Kageyana/RX671_MCR/RX671_MCR/src/smc_gen/r_bsp/board/generic_rx671/r_bsp_config_reference.h

/*
* Copyright (c) 2011 Renesas Electronics Corporation and/or its affiliates
*
* SPDX-License-Identifier: BSD-3-Clause
*/
/***********************************************************************************************************************
* File Name    : r_bsp_config_reference.h
* Device(s)    : RX671
* Description  : The file r_bsp_config.h is used to configure your BSP. r_bsp_config.h should be included
*                somewhere in your package so that the r_bsp code has access to it. This file (r_bsp_config_reference.h)
*                is just a reference file that the user can use to make their own r_bsp_config.h file.
************************************************************************************************************************
* History : DD.MM.YYYY Version  Description
*         : 18.05.2021 1.00     First Release
*         : 30.11.2021 1.01     Added the following macro definition.
*                               - BSP_CFG_CONFIGURATOR_VERSION
*                               - BSP_CFG_CPLUSPLUS
*                               - BSP_CFG_SERIAL_PROGRAMMER_CONECT_ENABLE
*                               - BSP_CFG_ONCHIP_DEBUGGER_CONECT_ENABLE
*                               Changed initial value of the following macro definitions.
*                               - BSP_CFG_MCU_PART_GROUP
*                               - BSP_CFG_MCU_PART_SERIES
*         : 11.02.2022 1.02     Changed initial value of the following macro definitions.
*                               - BSP_CFG_SWINT_UNIT1_ENABLE
*                               - BSP_CFG_SWINT_UNIT2_ENABLE
*         : 25.11.2022 1.03     Modified comment.
*         : 28.02.2023 1.04     Modified comment.
*         : 21.11.2023 1.05     Added the following macro definitions.
*                               - BSP_CFG_BUS_PRIORITY_INITIALIZE_ENABLE
*                               - BSP_CFG_MEMORY_BUS1_PRIORITY
*                               - BSP_CFG_MEMORY_BUS2_PRIORITY
*                               - BSP_CFG_INTERNAL_PERIPHERAL_BUS1_PRIORITY
*                               - BSP_CFG_INTERNAL_PERIPHERAL_BUS2_3_PRIORITY
*                               - BSP_CFG_INTERNAL_PERIPHERAL_BUS4_5_PRIORITY
*                               - BSP_CFG_INTERNAL_PERIPHERAL_BUS6_PRIORITY
*                               - BSP_CFG_EXTERNAL_BUS_PRIORITY
*                               - BSP_CFG_INTERNAL_EXPANSION_BUS_PRIORITY
*                               - BSP_CFG_BOOTLOADER_PROJECT
*         : 27.11.2024 1.06     Changed comment of BSP_CFG_RTC_ENABLE.
*         : 26.02.2025 1.07     Changed the disclaimer.
***********************************************************************************************************************/
#ifndef R_BSP_CONFIG_REF_HEADER_FILE
#define R_BSP_CONFIG_REF_HEADER_FILE

/***********************************************************************************************************************
Configuration Options
***********************************************************************************************************************/

/* NOTE:
   The default settings are the same as when using RSKRX671.
   Change to the settings for the user board.
*/

/* Start up select
   0 = Enable BSP startup program.
   1 = Disable BSP startup program. (e.g. Using user startup program.)
   NOTE: This setting is available only when using CCRX. */
#define BSP_CFG_STARTUP_DISABLE (0)

/* Enter the product part number for your MCU. This information will be used to obtain information about your MCU such 
   as package and memory size.
   To help parse this information, the part number will be defined using multiple macros.
   R 5 F 56 71 E D D FB
   | | | |  |  | | | |  Macro Name                             Description
   | | | |  |  | | | |__BSP_CFG_MCU_PART_PACKAGE             = Package type, number of pins, and pin pitch
   | | | |  |  | | |____not used                             = Products with wide temperature range
   | | | |  |  | |______BSP_CFG_MCU_PART_FUNCTION            = Encryption module included/not included
   | | | |  |  |________BSP_CFG_MCU_PART_MEMORY_SIZE         = ROM, RAM, and Data Flash Capacity
   | | | |  |___________BSP_CFG_MCU_PART_GROUP               = Group name
   | | | |______________BSP_CFG_MCU_PART_SERIES              = Series name
   | | |________________BSP_CFG_MCU_PART_MEMORY_TYPE         = Type of memory (Flash, ROMless)
   | |__________________not used                             = Renesas MCU
   |____________________not used                             = Renesas semiconductor product.
*/

/* Package type. Set the macro definition based on values below:
   Character(s) = Value for macro = Package Type/Number of Pins/Pin Pitch
   LE           = 0x0             = TFLGA/145/0.65
   FB           = 0x3             = LFQFP/144/0.50
   LK           = 0x4             = TFLGA/145/0.50
   FP           = 0x5             = LFQFP/100/0.50
   NE           = 0x7             = HWQFN/48/0.50
   FM           = 0x8             = LFQFP/64/0.50
   LJ           = 0xA             = TFLGA/100/0.65
   BP           = 0xC             = TFBGA/64/0.50
*/
#define BSP_CFG_MCU_PART_PACKAGE        (0x3)

/* Whether Encryption is included or not.
   Character(s) = Value for macro = Description
   D            = 0xD             = Encryption module not included
   H            = 0x11            = Encryption module included
*/
#define BSP_CFG_MCU_PART_FUNCTION       (0xD)

/* ROM, RAM, and Data Flash Capacity.
   Character(s) = Value for macro = ROM Size/Ram Size/Data Flash Size
   9            = 0x9             = 1MB/384KB/8KB
   C            = 0xC             = 1.5MB/384KB/8KB
   E            = 0xE             = 2MB/384KB/8KB
*/
#define BSP_CFG_MCU_PART_MEMORY_SIZE    (0xE)

/* Group name.
   Character(s) = Description
   71           = RX671 Group
*/
#define BSP_CFG_MCU_PART_GROUP          "RX671"

/* Series name.
   Character(s) = Description
   56           = RX600 Series
*/
#define BSP_CFG_MCU_PART_SERIES         "RX600"

/* Memory type.
   Character(s) = Value for macro = Description
   F            = 0x0             = Flash memory version
*/
#define BSP_CFG_MCU_PART_MEMORY_TYPE    (0x0)

/* Whether to use 1 stack or 2. RX MCUs have the ability to use 2 stacks: an interrupt stack and a user stack.
 * When using 2 stacks the user stack will be used during normal user code. When an interrupt occurs the CPU
 * will automatically shift to using the interrupt stack. Having 2 stacks can make it easier to figure out how
 * much stack space to allocate since the user does not have to worry about always having enough room on the
 * user stack for if-and-when an interrupt occurs. Some users will not want 2 stacks though because it is not
 * needed in all applications and can lead to wasted RAM (i.e. space in between stacks that is not used).
 * If only 1 stack is used then the interrupt stack is the one that will be used. If 1 stack is chosen then
 * the user may want to remove the 'SU' section from the linker sections to remove any linker warnings.
 *
 * 0 = Use 1 stack. Disable user stack. User stack size set below will be ignored.
 * 1 = Use 2 stacks. User stack and interrupt stack will both be used.
 * NOTE: This setting is available only when using CCRX and GNUC.
 *       This is invalid when using Renesas RTOS with CCRX.
 */
#define BSP_CFG_USER_STACK_ENABLE       (1)

/* If only 1 stack is chosen using BSP_CFG_USER_STACK_ENABLE then no RAM will be allocated for the user stack. */
#if BSP_CFG_USER_STACK_ENABLE == 1
/* User Stack size in bytes.
 * NOTE: This setting is available only when using CCRX and GNUC.
 *       This is invalid when using Renesas RTOS with CCRX. */
#define BSP_CFG_USTACK_BYTES            (0x1000)
#endif

/* Interrupt Stack size in bytes.
   NOTE: This setting is available only when using CCRX and GNUC. */
#define BSP_CFG_ISTACK_BYTES            (0x400)

/* Heap size in bytes.
   To disable the heap you must follow these steps:
   1) Set this macro (BSP_CFG_HEAP_BYTES) to 0.
   2) Set the macro BSP_CFG_IO_LIB_ENABLE to 0.
   3) Disable stdio from being built into the project library. This is done by going into the Renesas RX Toolchain 
      settings and choosing the Standard Library section. After that choose 'Contents' in e2 studio.
      This will present a list of modules that can be included. Uncheck the box for stdio.h.
   NOTE: This setting is available only when using CCRX and GNUC. */
#define BSP_CFG_HEAP_BYTES              (0x400)

/* Initializes C input & output library functions.
   0 = Disable I/O library initialization in resetprg.c. If you are not using stdio then use this value.
   1 = Enable I/O library initialization in resetprg.c. This is default and needed if you are using stdio.
   NOTE: This setting is available only when using CCRX. */
#define BSP_CFG_IO_LIB_ENABLE           (1)

/* If desired the user may redirect the stdio charget() and/or charput() functions to their own respective functions
   by enabling below and providing and replacing the my_sw_... function names with the names of their own functions. */
#define BSP_CFG_USER_CHARGET_ENABLED    (0)
#define BSP_CFG_USER_CHARGET_FUNCTION     my_sw_charget_function

#define BSP_CFG_USER_CHARPUT_ENABLED    (0)
#define BSP_CFG_USER_CHARPUT_FUNCTION     my_sw_charput_function

/* After reset MCU will operate in Supervisor mode. To switch to User mode, set this macro to '1'. For more information
   on the differences between these 2 modes see the CPU >> Processor Mode section of your MCU's hardware manual.
   0 = Stay in Supervisor mode.
   1 = Switch to User mode.
   NOTE: This is invalid when using Renesas RTOS with CCRX.
*/
#define BSP_CFG_RUN_IN_USER_MODE        (0)

/* Set your desired ID code. NOTE, leave at the default (all 0xFF's) if you do not wish to use an ID code. If you set 
   this value and program it into the MCU then you will need to remember the ID code because the debugger will ask for 
   it when trying to connect. Note that the E1/E20 will ignore the ID code when programming the MCU during debugging.
   If you set this value and then forget it then you can clear the ID code by connecting up in serial boot mode using 
   FDT. The ID Code is 16 bytes long. The macro below define the ID Code in 4-byte sections. */
/* Lowest 4-byte section, address 0xFE7F5D50. From MSB to LSB: ID code 4, ID code 3, ID code 2, ID code 1/Control Code.
 */
#define BSP_CFG_ID_CODE_LONG_1          (0xFFFFFFFF)
/* 2nd ID Code section, address 0xFE7F5D54. From MSB to LSB: ID code 8, ID code 7, ID code 6, ID code 5. */
#define BSP_CFG_ID_CODE_LONG_2          (0xFFFFFFFF)
/* 3rd ID Code section, address 0xFE7F5D58. From MSB to LSB: ID code 12, ID code 11, ID code 10, ID code 9. */
#define BSP_CFG_ID_CODE_LONG_3          (0xFFFFFFFF)
/* 4th ID Code section, address 0xFE7F5D5C. From MSB to LSB: ID code 16, ID code 15, ID code 14, ID code 13. */
#define BSP_CFG_ID_CODE_LONG_4          (0xFFFFFFFF)

/* Select whether to enables or disables the connection of serial programmer.
   0 = Connection of a serial programmer is prohibited after a reset.
   1 = Connection of a serial programmer is permitted after a reset. (default)
*/
#define BSP_CFG_SERIAL_PROGRAMMER_CONECT_ENABLE   (1)

/* Select whether to enables or disables the connection of on-chip debugger.
   0 = Connection of an on-chip debugger is prohibited after a reset.
   1 = Connection of an on-chip debugger is permitted after a reset. (default)
*/
#define BSP_CFG_ONCHIP_DEBUGGER_CONECT_ENABLE   (1)

/* Select whether to oscillate the Main Clock Oscillator.
   0 = Stop Oscillating the Main Clock.
   1 = Enable oscillating the Main Clock. (default)
*/
#define BSP_CFG_MAIN_CLOCK_OSCILLATE_ENABLE    (1)

/* Select whether to oscillate the Sub Clock Oscillator.
   0 = Stop Oscillating the Sub Clock. (default)
   1 = Enable Oscillating the Sub Clock.
*/
#define BSP_CFG_SUB_CLOCK_OSCILLATE_ENABLE     (0)

/* Select whether to oscillate the High Speed On-Chip Oscillator (HOCO).
   0 = Stop Oscillating the HOCO. (default)
   1 = Enable Oscillating the HOCO.
*/
#define BSP_CFG_HOCO_OSCILLATE_ENABLE          (0)

/* Select whether to oscillate the Low Speed On-Chip Oscillator (LOCO).
   0 = Stop Oscillating the LOCO. (default)
   1 = Enable Oscillating the LOCO.
*/
#define BSP_CFG_LOCO_OSCILLATE_ENABLE          (0)

/* Select whether to oscillate the IWDT-Dedicated On-Chip Oscillator (IWDT).
   0 = Stop Oscillating the IWDT Clock. (default)
   1 = Enable Oscillating the IWDT Clock.
*/
#define BSP_CFG_IWDT_CLOCK_OSCILLATE_ENABLE    (0)

/* Clock source select (CKSEL).
   0 = Low Speed On-Chip Oscillator  (LOCO)
   1 = High Speed On-Chip Oscillator (HOCO)
   2 = Main Clock Oscillator
   3 = Sub-Clock Oscillator
   4 = PLL Circuit
*/
#define BSP_CFG_CLOCK_SOURCE            (4)

/* Main clock Oscillator Switching (MOSEL).
   0 = Resonator
   1 = External clock input
*/
#define BSP_CFG_MAIN_CLOCK_SOURCE       (0)

/* Select the source of the sub-clock provided to each module in the backup domain and the remote-control 
   signal receiver.(BKSCCR)
   0 = Internal sub-clock oscillator
   1 = External sub-clock oscillator
*/
#define BSP_CFG_BACKUP_DOMAIN_SUB_CLOCK_SOURCE    (0)

/* Configure clock source of clock output(CLKOUT) pin (CKOSEL).
   Available clock sources:
   0 = LOCO
   1 = HOCO
   2 = Main clock oscillator (default)
   3 = Sub-clock oscillator
   4 = PLL circuit
 */
#define BSP_CFG_CLKOUT_SOURCE           (2)

/* Defines whether to use the RTC or not.
   This setting will initialize the RTC related registers.
   0 = The RTC is not to be used.
   1 = The RTC is to be used.
   When using RTC FIT or RTC CG, the Smart Configurator sets this to "1". Set it to "1" when using RTC.
*/
#define BSP_CFG_RTC_ENABLE              (0)

/* Sub-Clock Oscillator Drive Capacity Control (RTCDV).
   0 = Drive capacity for standard CL. (default)
   1 = Drive capacity for low CL.
*/
#define BSP_CFG_SOSC_DRV_CAP            (0)

/* Clock configuration options.
   The input clock frequency is specified and then the system clocks are set by specifying the multipliers used. The
   multiplier settings are used to set the clock registers in resetprg.c. If a 24MHz clock is used and the
   ICLK is 120MHz, PCLKA is 120MHz, PCLKB is 60MHz, PCLKC is 60MHz, PCLKD is 60MHz, FCLK is 60MHz, USB Clock is 48MHz,
   and BCLK is 120MHz then the settings would be:

   BSP_CFG_XTAL_HZ  = 24000000
   BSP_CFG_PLL_DIV  = 1        (no division)
   BSP_CFG_PLL_MUL  = 10.0     (24MHz x 10.0 = 240MHz)
   BSP_CFG_ICK_DIV  = 2      : System Clock (ICLK)        = 
                               (((BSP_CFG_XTAL_HZ/BSP_CFG_PLL_DIV) * BSP_CFG_PLL_MUL) / BSP_CFG_ICK_DIV)  = 120MHz
   BSP_CFG_PCKA_DIV = 2      : Peripheral Clock A (PCLKA) = 
                               (((BSP_CFG_XTAL_HZ/BSP_CFG_PLL_DIV) * BSP_CFG_PLL_MUL) / BSP_CFG_PCKA_DIV) = 120MHz
   BSP_CFG_PCKB_DIV = 4      : Peripheral Clock B (PCLKB) = 
                               (((BSP_CFG_XTAL_HZ/BSP_CFG_PLL_DIV) * BSP_CFG_PLL_MUL) / BSP_CFG_PCKB_DIV) = 60MHz
   BSP_CFG_PCKC_DIV = 4      : Peripheral Clock C (PCLKC) = 
                               (((BSP_CFG_XTAL_HZ/BSP_CFG_PLL_DIV) * BSP_CFG_PLL_MUL) / BSP_CFG_PCKC_DIV) = 60MHz
   BSP_CFG_PCKD_DIV = 4      : Peripheral Clock D (PCLKD) = 
                               (((BSP_CFG_XTAL_HZ/BSP_CFG_PLL_DIV) * BSP_CFG_PLL_MUL) / BSP_CFG_PCKD_DIV) = 60MHz
   BSP_CFG_FCK_DIV  = 4      : Flash IF Clock (FCLK)      = 
                               (((BSP_CFG_XTAL_HZ/BSP_CFG_PLL_DIV) * BSP_CFG_PLL_MUL) / BSP_CFG_FCK_DIV)  = 60MHz
   BSP_CFG_BCK_DIV  = 2      : External Bus Clock (BCK)   = 
                               (((BSP_CFG_XTAL_HZ/BSP_CFG_PLL_DIV) * BSP_CFG_PLL_MUL) / BSP_CFG_BCK_DIV)  = 120MHz
   BSP_CFG_UCK_DIV  = 5      : USB Clock (UCLK)           = 
                               (((BSP_CFG_XTAL_HZ/BSP_CFG_PLL_DIV) * BSP_CFG_PLL_MUL) / BSP_CFG_UCK_DIV)  = 48MHz
*/

/* Input clock frequency in Hz (XTAL or EXTAL). */
#define BSP_CFG_XTAL_HZ                 (24000000)

/* The HOCO can operate at several different frequencies. Choose which one using the macro below.
   Available frequency settings:
   0 = 16MHz (default)
   1 = 18MHz
   2 = 20MHz
*/
#define BSP_CFG_HOCO_FREQUENCY          (0)

/* Select the frequency correction function of the HOCO.
   0 = Disable FLL of the HOCO. (default)
   1 = Enable FLL of the HOCO.
*/
#define BSP_CFG_HOCO_FLL_ENABLE         (0)

/* Select whether to initialize the HOCO trimming register.
   0 = Disable reset the HOCO trimming register in the initial setting process.
   1 = Enable reset the HOCO trimming register in the initial setting process.
   Note: The trimming value is adjusted at shipment on the specified conditions and the value after a reset varies 
         with the chips. When re-writing the HOCO trimming register, enable this macro definition.
*/
#define BSP_CFG_HOCO_TRIMMING_ENABLE    (0)

/* Set the frequency trimming value for the HOCO.
   0(Frequency: Low) - 511(Frequency: High)
   Note: The trimming value is adjusted at shipment on the specified conditions and the value after a reset varies 
         with the chips. When re-writing the HOCO trimming register, set this macro definition.
*/
#define BSP_CFG_HOCO_TRIMMING_REG_VALUE      (0)

/* PLL clock source (PLLSRCSEL). Choose which clock source to input to the PLL circuit.
   Available clock sources:
   0 = Main clock (default)
   1 = HOCO
*/
#define BSP_CFG_PLL_SRC                 (0)

/* PLL Input Frequency Division Ratio Select (PLIDIV).
   Available divisors = /1 (no division), /2, /3
*/
#define BSP_CFG_PLL_DIV                 (1)

/* PLL Frequency Multiplication Factor Select (STC).
   Available multipliers = x10.0 to x30.0 in 0.5 increments (e.g. 10.0, 10.5, 11.0, 11.5, ..., 29.0, 29.5, 30.0)
*/
#define BSP_CFG_PLL_MUL                 (10.0)

/* System Clock Divider (ICK).
   Available divisors = /1 (no division), /2, /4, /8, /16, /32, /64
*/
#define BSP_CFG_ICK_DIV                 (2)

/* Peripheral Module Clock A Divider (PCKA).
   Available divisors = /1 (no division), /2, /4, /8, /16, /32, /64
*/
#define BSP_CFG_PCKA_DIV                (2)

/* Peripheral Module Clock B Divider (PCKB).
   Available divisors = /1 (no division), /2, /4, /8, /16, /32, /64
*/
#define BSP_CFG_PCKB_DIV                (4)

/* Peripheral Module Clock C Divider (PCKC).
   Available divisors = /1 (no division), /2, /4, /8, /16, /32, /64
*/
#define BSP_CFG_PCKC_DIV                (4)

/* Peripheral Module Clock D Divider (PCKD).
   Available divisors = /1 (no division), /2, /4, /8, /16, /32, /64
*/
#define BSP_CFG_PCKD_DIV                (4)

/* External Bus Clock Divider (BCLK).
   Available divisors = /1 (no division), /2, /4, /8, /16, /32, /64
*/
#define BSP_CFG_BCK_DIV                 (2)

/* Flash IF Clock Divider (FCK).
   Available divisors = /1 (no division), /2, /4, /8, /16, /32, /64
*/
#define BSP_CFG_FCK_DIV                 (4)

/* USB Clock Divider Select.
   Available divisors = /2, /3, /4, /5
*/
#define BSP_CFG_UCK_DIV                 (5)

/* Configure BCLK output pin (only effective when external bus enabled)
   Values 0=no output, 1 = BCK frequency, 2= BCK/2 frequency
*/
#define BSP_CFG_BCLK_OUTPUT             (0)

/* Configure SDCLK output pin (only effective when external bus enabled)
   Values 0=no output, 1 = BCK frequency
*/
#define BSP_CFG_SDCLK_OUTPUT            (0)

/* CLKOUT Output Frequency Division Ratio Select. (CKODIV)
   Values
   0 = x1/1 (default)
   1 = x1/2
   2 = x1/4
   3 = x1/8
   4 = x1/16
 */
#define BSP_CFG_CLKOUT_DIV              (0)

/* Configure clock output(CLKOUT) pin (CKOSTP).
   Values
   0 = CLKOUT pin output stopped. (Fixed to the low level) (default)
   1 = CLKOUT pin output enabled.
 */
#define BSP_CFG_CLKOUT_OUTPUT           (0)

/* Main Clock Oscillator Wait Time (MOSCWTCR).
   The value of MOSCWTCR register required for correspondence with the waiting time required to secure stable 
   oscillation by the main clock oscillator is obtained by using the maximum frequency for fLOCO in the formula below.

   BSP_CFG_MOSC_WAIT_TIME > (tMAINOSC * (fLOCO_max) + 16)/32
   (tMAINOSC: main clock oscillation stabilization time; fLOCO_max: maximum frequency for fLOCO)

   If tMAINOSC is 9.98 ms and fLOCO_max is 264 kHz (the period is 1/3.78 us), the formula gives 
   BSP_CFG_MOSC_WAIT_TIME > (9.98 ms * (264 kHZ) + 16)/32 = 82.83, so set the BSP_CFG_MOSC_WAIT_TIME to 83(53h).

   NOTE: The waiting time is not required when an external clock signal is input for the main clock oscillator.
         Set the BSP_CFG_MOSC_WAIT_TIME to 00h.
*/
#define BSP_CFG_MOSC_WAIT_TIME          (0x53)

/* Sub-Clock Oscillator Wait Time (SOSCWTCR).
   The value of SOSCWTCR register required for correspondence with the expected time to secure settling of oscillation
   by the sub-clock oscillator is obtained by using the maximum frequency for fLOCO in the formula below.

   BSP_CFG_SOSC_WAIT_TIME > (tSUBOSC * (fLOCO_max) + 16)/16384
   (tSUBOSC: sub-clock oscillation stabilization time; fLOCO_max: maximum frequency for fLOCO)

   If tSUBOSC is 2 s and fLOCO is 264 kHz (the period is 1/3.78 us), the formula gives
    BSP_CFG_SOSC_WAIT_TIME > (2 s * (264 kHz) +16)/16384 = 32.22, so set the  BSP_CFG_SOSC_WAIT_TIME bits to 33(21h).
*/
#define BSP_CFG_SOSC_WAIT_TIME          (0x21)

/* ROM Cache Enable Register (ROMCE).
   0 = ROM cache operation disabled.
   1 = ROM cache operation enabled.
*/
#define BSP_CFG_ROM_CACHE_ENABLE        (1)

/* Configure non-cacheable area 0 of the ROM cache function.
   0 = Non-cacheable area 0 settings disabled.
   1 = Non-cacheable area 0 settings enabled.
*/
#define BSP_CFG_NONCACHEABLE_AREA0_ENABLE    (0)

/* Specifies the start address of non-cacheable area 0.
   Selects the start address of non-cacheable area 0.
   The upper 10 bits are fixed at 1. The lower 4 bits are fixed at 0.
*/
#define BSP_CFG_NONCACHEABLE_AREA0_ADDR      (0xFFF00000)

/* Configures the size of non-cacheable area 0.
   Selects the size of non-cacheable area 0 in byte units from among the following:
   0x0 =  16 bytes, 0xA =  16K bytes,
   0x1 =  32 bytes, 0xB =  32K bytes,
   0x2 =  64 bytes, 0xC =  64K bytes,
   0x3 = 128 bytes, 0xD = 128K bytes,
   0x4 = 256 bytes, 0xE = 256K bytes,
   0x5 = 512 bytes, 0xF = 512K bytes,
   0x6 =  1K bytes, 0x10=   1M bytes,
   0x7 =  2K bytes,
   0x8 =  4K bytes,
   0x9 =  8K bytes
*/
#define BSP_CFG_NONCACHEABLE_AREA0_SIZE      (0x0)

/* Specifies the IF non-cacheable area enable bit setting of non-cacheable area 0.
   0 = Non-cacheable area 0 setting of IF cache disabled.
   1 = Non-cacheable area 0 setting of IF cache enabled.
*/
#define BSP_CFG_NONCACHEABLE_AREA0_IF_ENABLE (1)

/* Specifies the OA non-cacheable area enable bit setting of non-cacheable area 0.
   0 = Non-cacheable area 0 setting of OA cache disabled.
   1 = Non-cacheable area 0 setting of OA cache enabled.
*/
#define BSP_CFG_NONCACHEABLE_AREA0_OA_ENABLE (1)

/* Specifies the DM non-cacheable area enable bit setting of non-cacheable area 0.
   0 = Non-cacheable area 0 setting of DM cache disabled.
   1 = Non-cacheable area 0 setting of DM cache enabled.
*/
#define BSP_CFG_NONCACHEABLE_AREA0_DM_ENABLE (1)

/* Configure non-cacheable area 1 of the ROM cache function.
   0 = Non-cacheable area 1 settings disabled.
   1 = Non-cacheable area 1 settings enabled.
*/
#define BSP_CFG_NONCACHEABLE_AREA1_ENABLE    (0)

/* Specifies the start address of non-cacheable area 1.
   Selects the start address of non-cacheable area 1.
   The upper 10 bits are fixed at 1. The lower 4 bits are fixed at 0.
*/
#define BSP_CFG_NONCACHEABLE_AREA1_ADDR      (0xFFF00000)

/* Configures the size of non-cacheable area 1.
   Selects the size of non-cacheable area 0 in byte units from among the following:
   0x0 =  16 bytes, 0xA =  16K bytes,
   0x1 =  32 bytes, 0xB =  32K bytes,
   0x2 =  64 bytes, 0xC =  64K bytes,
   0x3 = 128 bytes, 0xD = 128K bytes,
   0x4 = 256 bytes, 0xE = 256K bytes,
   0x5 = 512 bytes, 0xF = 512K bytes,
   0x6 =  1K bytes, 0x10=   1M bytes,
   0x7 =  2K bytes,
   0x8 =  4K bytes,
   0x9 =  8K bytes
*/
#define BSP_CFG_NONCACHEABLE_AREA1_SIZE      (0x0)

/* Specifies the IF non-cacheable area enable bit setting of non-cacheable area 1.
   0 = Non-cacheable area 1 setting of IF cache disabled.
   1 = Non-cacheable area 1 setting of IF cache enabled.
*/
#define BSP_CFG_NONCACHEABLE_AREA1_IF_ENABLE (1)

/* Specifies the OA non-cacheable area enable bit setting of non-cacheable area 1.
   0 = Non-cacheable area 1 setting of OA cache disabled.
   1 = Non-cacheable area 1 setting of OA cache enabled.
*/
#define BSP_CFG_NONCACHEABLE_AREA1_OA_ENABLE (1)

/* Specifies the DM non-cacheable area enable bit setting of non-cacheable area 1.
   0 = Non-cacheable area 1 setting of DM cache disabled.
   1 = Non-cacheable area 1 setting of DM cache enabled.
*/
#define BSP_CFG_NONCACHEABLE_AREA1_DM_ENABLE (1)

/* Configure WDT and IWDT settings.
   OFS0 - Option Function Select Register 0
       b31:b29 Reserved When reading, these bits return the value written by the user. The write value should be 1.
       b28     WDTRSTIRQS - WDT Reset Interrupt Request - What to do on underflow (0=take interrupt, 1=reset MCU)
       b27:b26 WDTRPSS   - WDT Window Start Position Select - (0=25%, 1=50%, 2=75%, 3=100%,don't use)
       b25:b24 WDTRPES   - WDT Window End Position Select - (0=75%, 1=50%, 2=25%, 3=0%,don't use)
       b23:b20 WDTCKS    - WDT Clock Frequency Division Ratio - (1=PCLKB/4, 4=PCLKB/64, 0xF=PCLKB/128, 6=PCLKB/256,
                                                                 7=PCLKB/2048, 8=PCLKB/8192)
       b19:b18 WDTTOPS   - WDT Timeout Period Select (0=1024 cycles, 1=4096, 2=8192, 3=16384)
       b17     WDTSTRT   - WDT Start Mode Select - (0=auto-start after reset, 1=halt after reset)
       b16:b15 Reserved (set to 1)
       b14     IWDTSLCSTP - IWDT Sleep Mode Count Stop Control - (0=can't stop count, 1=stop w/some low power modes)
       b13     Reserved (set to 1)
       b12     IWDTRSTIRQS - IWDT Reset Interrupt Request - What to do on underflow (0=take interrupt, 1=reset MCU)
       b11:b10 IWDTRPSS - IWDT Window Start Position Select - (0=25%, 1=50%, 2=75%, 3=100%,don't use)
       b9:b8   IWDTRPES - IWDT Window End Position Select - (0=75%, 1=50%, 2=25%, 3=0%,don't use)
       b7:b4   IWDTCKS - IWDT Clock Frequency Division Ratio - (0=none, 2=/16, 3 = /32, 4=/64, 0xF=/128, 5=/256)
       b3:b2   IWDTTOPS - IWDT Timeout Period Select - (0=1024 cycles, 1=4096, 2=8192, 3=16384)
       b1      IWDTSTRT - IWDT Start Mode Select - (0=auto-start after reset, 1=halt after reset)
       b0      Reserved (set to 1)
   Default value is 0xFFFFFFFF.
*/
#define BSP_CFG_OFS0_REG_VALUE  (0xFFFFFFFF)

/* Configure whether voltage detection 0 circuit and HOCO are enabled after reset.
   OFS1 - Option Function Select Register 1
       b31:b9 Reserved (set to 1)
       b8     HOCOEN - Enable/disable HOCO oscillation after a reset (0=enable, 1=disable)
       b7:b3  Reserved When reading, these bits return the value written by the user. The write value should be 1.
       b2     LVDAS - Voltage Detection 0 circuit start (1=monitoring disabled)
       b1:b0  VDSEL - Voltage Detection 0 level select (1=2.94v, 2=2.87v, 3=2.80v)
       NOTE: If HOCO oscillation is enabled by OFS1.HOCOEN, HOCO frequency is 16MHz and FLL is disabled.
             BSP_CFG_HOCO_FREQUENCY should be default value and BSP_CFG_HOCO_FLL_ENABLE should be 0.
   Default value is 0xFFFFFFFF.
*/
#define BSP_CFG_OFS1_REG_VALUE  (0xFFFFFFFF)

/* Trusted memory is facility to prevent the reading of blocks 8 and 9 and blocks 46 and 47 (in dual mode) in 
   the code flash memory by third party software. This feature is disabled by default.
   TMEF - TM Enable Flag Register
       b31     Reserved (set to 1)
       b30:b28 TMEFDB - Dual-Bank TM Enable - 000: The TM function in the address range from FFEE 0000h to 
                                                   FFEE FFFFh is enabled in dual mode.
                                            - 111: The TM function in the address range from FFEE 0000h to 
                                                   FFEE FFFFh is disabled in dual mode.
       b27     Reserved (set to 1)
       b26:b24 TMEF   - TM Enable - 000: TM function is enabled.
                                  - 111: TM function is disabled.
       b23:b0  Reserved (set to 1)
   Default value is 0xFFFFFFFF.
*/
#define BSP_CFG_TRUSTED_MODE_FUNCTION  (0xFFFFFFFF)

/* Configure FAW register is used to set the write protection flag and boot area select flag 
   for setting the flash access window startaddress and flash access window end address.
   FAW - Flash Access Window Setting Register
       b31      BTFLG - Boot Area Select Flag - 0: FFFF C000h to FFFF DFFFh are used as the boot area
                                              - 1: FFFF E000h to FFFF FFFFh are used as the boot area
       b30:b28  Reserved - When reading, these bits return the value written by the user.The write value should be 1.
       b27:b16  FAWE - Flash Access Window End Address - Flash access window end address
       b15      FSPR - Access Window Protection Flag - 0: With protection (P/E disabled)
                                                     - 1: Without protection (P/E enabled)
       b14:b12  Reserved - When reading, these bits return the value written by the user.The write value should be 1.
       b11:b0   FAWS - Flash Access Window Start Address - Flash access window start address 
       NOTE: Once 0 is written to this bit, the bit can never be restored to 1.
             Therefore, the access window and the BTFLG bit never be set again or the TM function 
             never be disabled once it has been enabled.
             Exercise extra caution when handling the FSPR bit.
   Default value is 0xFFFFFFFF.
*/
#define BSP_CFG_FAW_REG_VALUE  (0xFFFFFFFF)

/* The ROM code protection register is a function to prohibit reading from or programming to the flash memory
   when the flash programmer is used during off-board programming.
   ROMCODE - ROM Code Protection Register
       b31:b0  ROM Code - 0000 0000h: ROM code protection enabled (ROM code protection 1).
                          0000 0001h: ROM code protection enabled (ROM code protection 2).
                          Other than above: ROM code protection disabled.
       Note: The ROMCODE register should be set in 32-bit units.
   Default value is 0xFFFFFFFF.
*/
#define BSP_CFG_ROMCODE_REG_VALUE  (0xFFFFFFFF)

/* Select the bank mode of dual-bank function of the code flash memory.
   0 = Dual mode.
   1 = Linear mode. (default)
   NOTE: If the dual bank function has been incorporated in a device, select the bank mode in this macro.
         Default setting of the bank mode is linear mode.
         If the dual bank function has not been incorporated in a device, this macro should be 1.
*/
#define BSP_CFG_CODE_FLASH_BANK_MODE    (1)

/* Select the startup bank of the program when dual bank function is in dual mode.
   0 = The address range of bank 1 from FFE00000h to FFEFFFFFh and bank 0 from FFF00000h to FFFFFFFFh. (default)
   1 = The address range of bank 1 from FFF00000h to FFFFFFFFh and bank 0 from FFE00000h to FFEFFFFFh.
   NOTE: If the dual bank function has been incorporated in a device, select the start bank in this macro.
         Default setting of the start bank is bank0.
         If the dual bank function has not been incorporated in a device, this macro should be 0.
*/
#define BSP_CFG_CODE_FLASH_START_BANK   (0)

/* This macro lets other modules no if a RTOS is being used.
   0 = RTOS is not used.
   1 = FreeRTOS is used.
   2 = embOS is used.(This is not available.)
   3 = MicroC_OS is used.(This is not available.)
   4 = Renesas ITRON OS (RI600V4 or RI600PX) is used.
   5 = Azure RTOS is used.
*/
#define BSP_CFG_RTOS_USED               (0)

/* This macro is used to select which Renesas ITRON OS.
   0 = RI600V4 is used.
   1 = RI600PX is used.
*/
#define BSP_CFG_RENESAS_RTOS_USED       (0)

/* This macro is used to select which CMT channel used for system timer of RTOS.
 * The setting of this macro is only valid if the macro BSP_CFG_RTOS_USED is set to a value other than 0. */
#if BSP_CFG_RTOS_USED != 0
/* Setting value.
 * 0      = CMT channel 0 used for system timer of RTOS (recommended to be used for RTOS).
 * 1      = CMT channel 1 used for system timer of RTOS.
 * 2      = CMT channel 2 used for system timer of RTOS.
 * 3      = CMT channel 3 used for system timer of RTOS.
 * Others = Invalid.
 * NOTE: This is invalid when using Renesas RTOS with CCRX.
 */
#define BSP_CFG_RTOS_SYSTEM_TIMER       (0)
#endif

/* By default modules will use global locks found in mcu_locks.c. If the user is using a RTOS and would rather use its
   locking mechanisms then they can change this macro.
   NOTE: If '1' is chosen for this macro then the user must also change the next macro 'BSP_CFG_USER_LOCKING_TYPE'.
   0 = Use default locking (non-RTOS)
   1 = Use user defined locking mechanism.
*/
#define BSP_CFG_USER_LOCKING_ENABLED    (0)

/* If the user decides to use their own locking mechanism with FIT modules then they will need to redefine the typedef
   that is used for the locks. If the user is using a RTOS then they would likely redefine the typedef to be 
   a semaphore/mutex type of their RTOS. Use the macro below to set the type that will be used for the locks.
   NOTE: If BSP_CFG_USER_LOCKING_ENABLED == 0 then this typedef is ignored.
   NOTE: Do not surround the type with parentheses '(' ')'.
*/
#define BSP_CFG_USER_LOCKING_TYPE       bsp_lock_t

/* If the user decides to use their own locking mechanism with FIT modules then they will need to define the functions
   that will handle the locking and unlocking. These functions should be defined below.
   If BSP_CFG_USER_LOCKING_ENABLED is != 0:
   R_BSP_HardwareLock(mcu_lock_t hw_index) will call BSP_CFG_USER_LOCKING_HW_LOCK_FUNCTION(mcu_lock_t hw_index)
   R_BSP_HardwareUnlock(mcu_lock_t hw_index) will call BSP_CFG_USER_LOCKING_HW_UNLOCK_FUNCTION(mcu_lock_t hw_index)
       NOTE:With these functions the index into the array holding the global hardware locks is passed as the parameter.
   R_BSP_SoftwareLock(BSP_CFG_USER_LOCKING_TYPE * plock) will call 
   BSP_CFG_USER_LOCKING_SW_LOCK_FUNCTION(BSP_CFG_USER_LOCKING_TYPE * plock)
   R_BSP_SoftwareUnlock(BSP_CFG_USER_LOCKING_TYPE * plock) will call 
   BSP_CFG_USER_LOCKING_SW_UNLOCK_FUNCTION(BSP_CFG_USER_LOCKING_TYPE * plock)
       NOTE:With these functions the actual address of the lock to use is passed as the parameter.
   NOTE: These functions must return a boolean. If lock was obtained or released successfully then return true. Else, 
         return false.
   NOTE: If BSP_CFG_USER_LOCKING_ENABLED == 0 then this typedef is ignored.
   NOTE: Do not surround the type with parentheses '(' ')'.
*/
#define BSP_CFG_USER_LOCKING_HW_LOCK_FUNCTION      my_hw_locking_function
#define BSP_CFG_USER_LOCKING_HW_UNLOCK_FUNCTION    my_hw_unlocking_function
#define BSP_CFG_USER_LOCKING_SW_LOCK_FUNCTION      my_sw_locking_function
#define BSP_CFG_USER_LOCKING_SW_UNLOCK_FUNCTION    my_sw_unlocking_function

/* If the user would like to determine if a warm start reset has occurred, then they may enable one or more of the
   following callback definitions AND provide a call back function name for the respective callback
   function (to be defined by the user). Setting BSP_CFG_USER_WARM_START_CALLBACK_PRE_INITC_ENABLED = 1 will result
   in a callback to the user defined my_sw_warmstart_prec_function just prior to the initialization of the C
   runtime environment by resetprg.
   Setting BSP_CFG_USER_WARM_START_CALLBACK_POST_INITC_ENABLED = 1 will result in a callback to the user defined
   my_sw_warmstart_postc_function just after the initialization of the C runtime environment by resetprg.
*/
#define BSP_CFG_USER_WARM_START_CALLBACK_PRE_INITC_ENABLED    (0)
#define BSP_CFG_USER_WARM_START_PRE_C_FUNCTION     my_sw_warmstart_prec_function

#define BSP_CFG_USER_WARM_START_CALLBACK_POST_INITC_ENABLED    (0)
#define BSP_CFG_USER_WARM_START_POST_C_FUNCTION    my_sw_warmstart_postc_function

/* By default FIT modules will check input parameters to be valid. This is helpful during development but some users
   will want to disable this for production code. The reason for this would be to save execution time and code space.
   This macro is a global setting for enabling or disabling parameter checking. Each FIT module will also have its
   own local macro for this same purpose. By default the local macros will take the global value from here though
   they can be overridden. Therefore, the local setting has priority over this global setting. Disabling parameter
   checking should only used when inputs are known to be good and the increase in speed or decrease in code space is 
   needed.
   0 = Global setting for parameter checking is disabled.
   1 = Global setting for parameter checking is enabled (Default).
*/
#define BSP_CFG_PARAM_CHECKING_ENABLE               (1)

/* This macro is used to define the voltage that is supplied to the MCU (Vcc). This macro is defined in millivolts. This
   macro does not actually change anything on the MCU. Some FIT modules need this information so it is defined here. */
#define BSP_CFG_MCU_VCC_MV                          (3300)

/* Allow initialization of auto-generated peripheral initialization code by Smart Configurator tool.
   When not using the Smart Configurator, set the value of BSP_CFG_CONFIGURATOR_SELECT to 0.
   0 = Disabled (default)
   1 = Smart Configurator initialization code used
*/
#define BSP_CFG_CONFIGURATOR_SELECT                 (0)

/* Version number of Smart Configurator.
   This macro definition is updated by Smart Configurator.
*/
#define BSP_CFG_CONFIGURATOR_VERSION                (100)

/* For some BSP functions, it is necessary to ensure that, while these functions are executing, interrupts from other 
   FIT modules do not occur. By controlling the IPL, these functions disable interrupts that are at or below the 
   specified interrupt priority level.
   This macro sets the IPL. Range is 0x0 - 0xF.
   Please set this macro more than IPR for other FIT module interrupts.
   The default value is 0xF (maximum value).
   Don't change if there is no special processing with higher priority than all fit modules.
*/
#define BSP_CFG_FIT_IPL_MAX                         (0xF)

/* Defines if the battery backup function is enabled in the current application.
   0 = battery backup function is disabled.
   1 = battery backup function is enabled.
*/
#define BSP_CFG_VBATT_ENABLE                        (0)

/* Software Interrupt (SWINT).
   0 = Software interrupt is not used.
   1 = Software interrupt is used.
   NOTE: When this macro is set to 1, the software interrupt is initialized in bsp startup routine. 
*/
#define BSP_CFG_SWINT_UNIT1_ENABLE    (0)
#define BSP_CFG_SWINT_UNIT2_ENABLE    (0)

/* Software Interrupt Task Buffer Number.
   For software interrupt, this value is number of buffering user tasks.
   So user can increase this value if user system would have many software interrupt tasks
   and user system has enough buffer. This value requires 9 byte per task.
   NOTE: This setting is common to all units. It can not be set individually. 
         The maximum value is 254.
*/
#define BSP_CFG_SWINT_TASK_BUFFER_NUMBER     (8)

/* Initial value of the software interrupt priority.
   For software interrupt, this value is interrupt priority. Range is 0x0 - 0xF.
   NOTE: This setting is common to all units. It can not be set individually. 
         Please be careful that this setting is the initial value of the interrupt priority register(IPR).
         It is possible to dynamically change the IPR.
*/
#define BSP_CFG_SWINT_IPR_INITIAL_VALUE     (0x1)

/* This macro is used for serial terminal on the board selected by smart configurator.
   0 = SCI UART Terminal is disabled.
   1 = SCI UART Terminal is enabled.
*/
#define BSP_CFG_SCI_UART_TERMINAL_ENABLE         (0)

/* This macro is channel number for serial terminal.
*/
#define BSP_CFG_SCI_UART_TERMINAL_CHANNEL        (10)

/* This macro is bit-rate for serial terminal.
*/
#define BSP_CFG_SCI_UART_TERMINAL_BITRATE        (115200)

/* This macro is interrupt priority for serial terminal.
   0(low) - 15(high)
*/
#define BSP_CFG_SCI_UART_TERMINAL_INTERRUPT_PRIORITY   (15)

/* This macro is used for C++ project and updated by Smart Configurator.
   0 = This project is a C project.(Not a C++ project).
   1 = This project is a C++ project.
*/
#define BSP_CFG_CPLUSPLUS             (0)

/* Select whether to enable bus priority initialization.
   0 = Bus priority initialization is disabled.
   1 = Bus priority initialization is enabled.
*/
#define BSP_CFG_BUS_PRIORITY_INITIALIZE_ENABLE      (0)

/* Select the priority order for memory bus 1 (RAM).
   0 = The order of priority is fixed.
   1 = The order of priority is toggled.
*/
#define BSP_CFG_MEMORY_BUS1_PRIORITY                (0)

/* Select the priority order for memory bus 2 (code flash memory).
   0 = The order of priority is fixed.
   1 = The order of priority is toggled.
*/
#define BSP_CFG_MEMORY_BUS2_PRIORITY                (0)

/* Select the priority order for internal peripheral bus 1.
   0 = The order of priority is fixed.
   1 = The order of priority is toggled.
*/
#define BSP_CFG_INTERNAL_PERIPHERAL_BUS1_PRIORITY   (0)

/* Select the priority order for internal peripheral buses 2 and 3.
   0 = The order of priority is fixed.
   1 = The order of priority is toggled.
*/
#define BSP_CFG_INTERNAL_PERIPHERAL_BUS2_3_PRIORITY (0)

/* Select the priority order for internal peripheral buses 4 and 5.
   0 = The order of priority is fixed.
   1 = The order of priority is toggled.
*/
#define BSP_CFG_INTERNAL_PERIPHERAL_BUS4_5_PRIORITY (0)

/* Select the priority order for internal peripheral bus 6.
   0 = The order of priority is fixed.
   1 = The order of priority is toggled.
*/
#define BSP_CFG_INTERNAL_PERIPHERAL_BUS6_PRIORITY   (0)

/* Select the priority order for the external bus.
   0 = The order of priority is fixed.
   1 = The order of priority is toggled.
*/
#define BSP_CFG_EXTERNAL_BUS_PRIORITY               (0)

/* Select the priority order for internal expansion bus.
   0 = The order of priority is fixed.
   1 = The order of priority is toggled.
*/
#define BSP_CFG_INTERNAL_EXPANSION_BUS_PRIORITY     (0)

/* Select whether it is bootloader project.
   0 = This project isn't a bootloader project.
   1 = This project is a bootloader project.
   NOTE: Not normally used. Set this to "1" only in the bootloader project.
*/
#define BSP_CFG_BOOTLOADER_PROJECT    (0)

#endif /* R_BSP_CONFIG_REF_HEADER_FILE */
