Kageyana/RX671_MCR/RX671_MCR/src/smc_gen/general/r_cg_mtu3.h

/*
* Copyright (c) 2016 - 2025 Renesas Electronics Corporation and/or its affiliates
*
* SPDX-License-Identifier: BSD-3-Clause
*/

/***********************************************************************************************************************
* File Name        : r_cg_mtu3.h
* Version          : 1.0.50
* Device(s)        : R5F5671EHxLE
* Description      : General header file for MTU3 peripheral.
***********************************************************************************************************************/

#ifndef MTU3_H
#define MTU3_H

/***********************************************************************************************************************
Macro definitions (Register bit)
***********************************************************************************************************************/
/*
    Timer Control Register (TCR)
*/
/* Time Pre-scaler Select (TPSC[2:0]) */
#define _00_MTU_PCLK_1                  (0x00U) /* Internal clock: counts on PCLK/1 (for all channels) */
#define _01_MTU_PCLK_4                  (0x01U) /* Internal clock: counts on PCLK/4 (for all channels) */
#define _02_MTU_PCLK_16                 (0x02U) /* Internal clock: counts on PCLK/16 (for all channels) */
#define _03_MTU_PCLK_64                 (0x03U) /* Internal clock: counts on PCLK/64 (for all channels) */
#define _04_MTU_PCLK_256                (0x04U) /* Internal clock: counts on PCLK/256 (for MTU3,4,6,7,8) */
#define _06_MTU_PCLK_256                (0x06U) /* Internal clock: counts on PCLK/256 (for MTU1) */
#define _05_MTU_PCLK_1024               (0x05U) /* Internal clock: counts on PCLK/1024 (for MTU3,4,6,7,8) */
#define _07_MTU_PCLK_1024               (0x07U) /* Internal clock: counts on PCLK/1024 (for MTU2) */
#define _07_MTU_COUNT                   (0x07U) /* Counts on MTU2.TCNT overflow/underflow (for MTU1) */
#define _04_MTU_MTCLKA                  (0x04U) /* External clock: counts on MTCLKA pin input (for MTU0,1,2) */
#define _06_MTU_MTCLKA                  (0x06U) /* External clock: counts on MTCLKA pin input (for MTU3,4,6,7,8) */
#define _05_MTU_MTCLKB                  (0x05U) /* External clock: counts on MTCLKB pin input (for MTU0,1,2) */
#define _07_MTU_MTCLKB                  (0x07U) /* External clock: counts on MTCLKB pin input (for MTU3,4,6,7,8) */
#define _06_MTU_MTCLKC                  (0x06U) /* External clock: counts on MTCLKC pin input (for MTU0,2) */
#define _07_MTU_MTCLKD                  (0x07U) /* External clock: counts on MTCLKD pin input (for MTU0) */
/* Clock Edge Select (CKEG[1:0]) */
#define _00_MTU_CKEG_RISE               (0x00U) /* Count at rising edge */
#define _08_MTU_CKEG_FALL               (0x08U) /* Count at falling edge */
#define _10_MTU_CKEG_BOTH               (0x10U) /* Count at both edges */
/* Counter Clear Select (CCLR[2:0]) */
#define _00_MTU_CKCL_DIS                (0x00U) /* TCNT clearing disabled */
#define _20_MTU_CKCL_A                  (0x20U) /* TCNT cleared by TGRA compare match/input capture */
#define _40_MTU_CKCL_B                  (0x40U) /* TCNT cleared by TGRB compare match/input capture */
#define _60_MTU_CKCL_SYN                (0x60U) /* TCNT cleared by counter clearing in another synchronous channel */
#define _A0_MTU_CKCL_C                  (0xA0U) /* TCNT cleared by TGRC compare match/input capture */
#define _C0_MTU_CKCL_D                  (0xC0U) /* TCNT cleared by TGRD compare match/input capture */

/*
    Timer Control Register 2 (TCR2)
*/
/* Time Pre-scaler Select (TPSC2[2:0]) */
#define _01_MTU_PCLK_2                  (0x01U) /* Internal clock: counts on PCLK/2 (for all channels) */
#define _02_MTU_PCLK_8                  (0x02U) /* Internal clock: counts on PCLK/8 (for all channels) */
#define _03_MTU_PCLK_32                 (0x03U) /* Internal clock: counts on PCLK/32 (for all channels) */
#define _04_MTU_PCLK_256                (0x04U) /* Internal clock: counts on PCLK/256 (for MTU0,2,5) */
#define _04_MTU_PCLK_1024               (0x04U) /* Internal clock: counts on PCLK/1024 (for MTU1) */
#define _05_MTU_PCLK_1024               (0x05U) /* Internal clock: counts on PCLK/1024 (for MTU0,5) */
#define _07_MTU_MTIOC1A                 (0x07U) /* External clock: counts on MTIOC1A pin output (for MTU0,5) */
/* Phase Counting Mode Function Expansion Control (PCB[1:0]) */
#define _00_MTU_PCB_00                  (0x00U) /* Count condition 1 of phase counting mode 2,3,5 */
#define _08_MTU_PCB_01                  (0x08U) /* Count condition 2 of phase counting mode 2,3 */
#define _10_MTU_PCB_10                  (0x10U) /* Count condition 2 of phase counting mode 5 */
#define _18_MTU_PCB_11                  (0x18U) /* Count condition 3 of phase counting mode 2,3 */

/*
    Timer Mode Register 1 (TMDR1)
*/
/* Mode Select (MD[3:0]) */
#define _00_MTU_NORMAL                  (0x00U) /* Normal mode */
#define _02_MTU_PWM1                    (0x02U) /* PWM mode 1 */
#define _03_MTU_PWM2                    (0x03U) /* PWM mode 2 */
#define _04_MTU_COT1                    (0x04U) /* Phase counting mode 1 */
#define _05_MTU_COT2                    (0x05U) /* Phase counting mode 2 */
#define _06_MTU_COT3                    (0x06U) /* Phase counting mode 3 */
#define _07_MTU_COT4                    (0x07U) /* Phase counting mode 4 */
#define _08_MTU_REST                    (0x08U) /* Reset-synchronized PWM mode */
#define _09_MTU_COT5                    (0x09U) /* Phase counting mode 5 */
#define _0D_MTU_CMT1                    (0x0DU) /* Complementary PWM mode 1 (transfer at crest) */
#define _0E_MTU_CMT2                    (0x0EU) /* Complementary PWM mode 2 (transfer at trough) */
#define _0F_MTU_CMT3                    (0x0FU) /* Complementary PWM mode 3 (transfer at crest and trough) */
/* Buffer Operation A (BFA) */
#define _00_MTU_BFA_NORMAL              (0x00U) /* TGRA and TGRC operate normally */
#define _10_MTU_BFA_BUFFER              (0x10U) /* TGRA and TGRC used together for buffer operation */
/* Buffer Operation B (BFB) */
#define _00_MTU_BFB_NORMAL              (0x00U) /* TGRB and TGRD operate normally */
#define _20_MTU_BFB_BUFFER              (0x20U) /* TGRB and TGRD used together for buffer operation */
/* Buffer Operation E (BFE) */
#define _00_MTU_BFE_NORMAL              (0x00U) /* MTU0.TGRE and MTU0.TGRF operate normally */
#define _40_MTU_BFE_BUFFER              (0x40U) /* MTU0.TGRE and MTU0.TGRF used together for buffer operation */

/*
    Timer Mode Registers 2 (TMDR2A and TMDR2B)
*/
/* Double Buffer Select (DRS) */
#define _00_MTU_DRS_DISABLE             (0x00U) /* Double buffer function is disabled */
#define _01_MTU_DRS_ENABLE              (0x01U) /* Double buffer function is enabled */

/*
    Timer I/O Control Register (TIOR)
*/
/* I/O Control A (IOA[3:0]) */
#define _00_MTU_IOA_DISABLE             (0x00U) /* Output prohibited */
#define _01_MTU_IOA_LL                  (0x01U) /* Initial output is low. Low output at compare match */
#define _02_MTU_IOA_LH                  (0x02U) /* Initial output is low. High output at compare match */
#define _03_MTU_IOA_LT                  (0x03U) /* Initial output is low. Toggle output at compare match */
#define _05_MTU_IOA_HL                  (0x05U) /* Initial output is high. Low output at compare match */
#define _06_MTU_IOA_HH                  (0x06U) /* Initial output is high. High output at compare match */
#define _07_MTU_IOA_HT                  (0x07U) /* Initial output is high. Toggle output at compare match */
#define _08_MTU_IOA_IR                  (0x08U) /* Input capture at rising edge */
#define _09_MTU_IOA_IF                  (0x09U) /* Input capture at falling edge */
#define _0A_MTU_IOA_IB                  (0x0AU) /* Input capture at both edges */
#define _0C_MTU_IOA_EX                  (0x0CU) /* Input capture at MTU1.TCNT up-count/down-count */
#define _0D_MTU_IOA_TGRA                (0x0DU) /* Input capture at MTU0.TGRA compare match/input capture */
#define _0E_MTU_IOA_TGRC                (0x0EU) /* Input capture at MTU8.TGRC compare match */
/* I/O Control B (IOB[3:0]) */
#define _00_MTU_IOB_DISABLE             (0x00U) /* Output prohibited */
#define _10_MTU_IOB_LL                  (0x10U) /* Initial output is low. Low output at compare match */
#define _20_MTU_IOB_LH                  (0x20U) /* Initial output is low. High output at compare match */
#define _30_MTU_IOB_LT                  (0x30U) /* Initial output is low. Toggle output at compare match */
#define _50_MTU_IOB_HL                  (0x50U) /* Initial output is high. Low output at compare match */
#define _60_MTU_IOB_HH                  (0x60U) /* Initial output is high. High output at compare match */
#define _70_MTU_IOB_HT                  (0x70U) /* Initial output is high. Toggle output at compare match */
#define _80_MTU_IOB_IR                  (0x80U) /* Input capture at rising edge */
#define _90_MTU_IOB_IF                  (0x90U) /* Input capture at falling edge */
#define _A0_MTU_IOB_IB                  (0xA0U) /* Input capture at both edges */
#define _C0_MTU_IOB_EX                  (0xC0U) /* Input capture at MTU1.TCNT up-count/down-count */
#define _C0_MTU_IOB_TGRC0               (0xC0U) /* Input capture at MTU0.TGRC compare match/input capture */
#define _E0_MTU_IOB_TGRC8               (0xE0U) /* Input capture at MTU8.TGRC compare match */
/* I/O Control C (IOC[3:0]) for MTU0.TIORL, MTU3.TIORL, MTU4.TIORL, MTU6.TIORL, MTU7.TIORL, MTU8.TIORL */
#define _00_MTU_IOC_DISABLE             (0x00U) /* Output prohibited */
#define _01_MTU_IOC_LL                  (0x01U) /* Initial output is low. Low output at compare match */
#define _02_MTU_IOC_LH                  (0x02U) /* Initial output is low. High output at compare match */
#define _03_MTU_IOC_LT                  (0x03U) /* Initial output is low. Toggle output at compare match */
#define _05_MTU_IOC_HL                  (0x05U) /* Initial output is high. Low output at compare match */
#define _06_MTU_IOC_HH                  (0x06U) /* Initial output is high. High output at compare match */
#define _07_MTU_IOC_HT                  (0x07U) /* Initial output is high. Toggle output at compare match */
#define _08_MTU_IOC_IR                  (0x08U) /* Input capture at rising edge */
#define _09_MTU_IOC_IF                  (0x09U) /* Input capture at falling edge */
#define _0A_MTU_IOC_IB                  (0x0AU) /* Input capture at both edges */
#define _0C_MTU_IOC_EX                  (0x0CU) /* Input capture at MTU1.TCNT up-count/down-count */
/* I/O Control C (IOC[4:0]) for MTU5.TIORU, MTU5.TIORV, MTU5.TIORW */
#define _00_MTU5_IOC_CP                 (0x00U) /* No function */
#define _11_MTU5_IOC_R                  (0x11U) /* Input capture at rising edge */
#define _12_MTU5_IOC_F                  (0x12U) /* Input capture at falling edge */
#define _13_MTU5_IOC_B                  (0x13U) /* Input capture at both edges */
#define _14_MTU5_IOC_TGRC               (0x14U) /* Input capture at MTU8.TGRC compare match */
#define _19_MTU5_IOC_PWM_LOW_TROUGH     (0x19U) /* Low pulse input signal. Capture at trough in 
                                                   complementary PWM mode */
#define _1A_MTU5_IOC_PWM_LOW_CREST      (0x1AU) /* Low pulse input signal. Capture at crest of 
                                                   complementary PWM mode */
#define _1B_MTU5_IOC_PWM_LOW_BOTH       (0x1BU) /* Low pulse input signal. Capture at crest and trough of 
                                                   complementary PWM mode */
#define _1D_MTU5_IOC_PWM_HIGH_TROUGH    (0x1DU) /* High pulse input signal. Capture at trough in 
                                                   complementary PWM mode */
#define _1E_MTU5_IOC_PWM_HIGH_CREST     (0x1EU) /* High pulse input signal. Capture at crest of 
                                                   complementary PWM mode */
#define _1F_MTU5_IOC_PWM_HIGH_BOTH      (0x1FU) /* High pulse input signal. Capture at crest and trough of 
                                                   complementary PWM mode */
/* I/O Control D (IOD[3:0]) for MTU0.TIORL, MTU3.TIORL, MTU4.TIORL, MTU6.TIORL, MTU7.TIORL, MTU8.TIORL */
#define _00_MTU_IOD_DISABLE             (0x00U) /* Output prohibited */
#define _10_MTU_IOD_LL                  (0x10U) /* Initial output is low. Low output at compare match */
#define _20_MTU_IOD_LH                  (0x20U) /* Initial output is low. High output at compare match */
#define _30_MTU_IOD_LT                  (0x30U) /* Initial output is low. Toggle output at compare match */
#define _50_MTU_IOD_HL                  (0x50U) /* Initial output is high. Low output at compare match */
#define _60_MTU_IOD_HH                  (0x60U) /* Initial output is high. High output at compare match */
#define _70_MTU_IOD_HT                  (0x70U) /* Initial output is high. Toggle output at compare match */
#define _80_MTU_IOD_IR                  (0x80U) /* Input capture at rising edge */
#define _90_MTU_IOD_IF                  (0x90U) /* Input capture at falling edge */
#define _A0_MTU_IOD_IB                  (0xA0U) /* Input capture at both edges */
#define _C0_MTU_IOD_EX                  (0xC0U) /* Input capture at MTU1.TCNT up-count/down-count */

/*
    Timer Buffer Operation Transfer Mode Register (TBTM)
*/
/* Timing Select A (TTSA) */
#define _00_MTU_TTSA_CMMA               (0x00U) /* When compare match A occurs in each channel, data is transferred */
#define _01_MTU_TTSA_TCNT               (0x01U) /* When TCNT is cleared in each channel, data is transferred */
/* Timing Select B (TTSB) */
#define _00_MTU_TTSB_CMMB               (0x00U) /* When compare match B occurs in each channel, data is transferred */
#define _02_MTU_TTSB_TCNT               (0x02U) /* When TCNT is cleared in each channel, data is transferred */
/* Timing Select E (TTSE) */
#define _00_MTU_TTSE_CMME               (0x00U) /* When compare match E occurs in MTU0, data is transferred */
#define _04_MTU_TTSE_TCNT               (0x04U) /* When MTU0.TCNT is cleared in MTU0, data is transferred */

/*
    Timer Input Capture Control Register (TICCR)
*/
/* Input Capture Enable (I1AE) */
#define _00_MTU_I1AE_DISABLE            (0x00U) /* Does not include MTIOC1A pin in MTU2.TGRA input capture condition */
#define _01_MTU_I1AE_ENABLE             (0x01U) /* Includes MTIOC1A pin in MTU2.TGRA input capture condition */
/* Input Capture Enable (I1BE) */
#define _00_MTU_I1BE_DISABLE            (0x00U) /* Does not include MTIOC1B pin in MTU2.TGRB input capture condition */
#define _02_MTU_I1BE_ENABLE             (0x02U) /* Includes MTIOC1B pin in MTU2.TGRB input capture condition */
/* Input Capture Enable (I2AE) */
#define _00_MTU_I2AE_DISABLE            (0x00U) /* Does not include MTIOC2A pin in MTU1.TGRA input capture condition */
#define _04_MTU_I2AE_ENABLE             (0x04U) /* Includes MTIOC2A pin in MTU1.TGRA input capture condition */
/* Input Capture Enable (I2BE) */
#define _00_MTU_I2BE_DISABLE            (0x00U) /* Does not include MTIOC2B pin in MTU1.TGRB input capture condition */
#define _08_MTU_I2BE_ENABLE             (0x08U) /* Includes MTIOC2B pin in MTU1.TGRB input capture condition */

/*
    Timer A/D Converter Start Request Control Register (TADCR)
*/
/* TCIVn Interrupt Skipping Link Enable (ITBnVE) (n=4,7) */
#define _0000_MTU_ITBVE_DISABLE         (0x0000U) /* TCInV interrupt skipping is not linked */
#define _0001_MTU_ITBVE_ENABLE          (0x0001U) /* TCInV interrupt skipping is linked */
/* TGIAn Interrupt Skipping Link Enable (ITBnAE) (n=3,6) */
#define _0000_MTU_ITBAE_DISABLE         (0x0000U) /* TGInA interrupt skipping is not linked */
#define _0002_MTU_ITBAE_ENABLE          (0x0002U) /* TGInA interrupt skipping is linked */
/* TCIVn Interrupt Skipping Link Enable (ITAnVE) (n=4,7) */
#define _0000_MTU_ITAVE_DISABLE         (0x0000U) /* TCInV interrupt skipping is not linked */
#define _0004_MTU_ITAVE_ENABLE          (0x0004U) /* TCInV interrupt skipping is linked */
/* TGIAn Interrupt Skipping Link Enable (ITAnAE) (n=3,6) */
#define _0000_MTU_ITAAE_DISABLE         (0x0000U) /* TGInA interrupt skipping is not linked */
#define _0008_MTU_ITAAE_ENABLE          (0x0008U) /* TGInA interrupt skipping is linked */
/* Down-Count TRGnBN Enable (DTnBE) */
#define _0000_MTU_DTBE_DISABLE          (0x0000U) /* A/D converter start request disabled during MTUn.TCNT down-count */
#define _0010_MTU_DTBE_ENABLE           (0x0010U) /* A/D converter start request enabled during MTUn.TCNT down-count */
/* Up-Count TRGnBN Enable (UTnBE) */
#define _0000_MTU_UTBE_DISABLE          (0x0000U) /* A/D converter start requests disabled during MTUn.TCNT up-count */
#define _0020_MTU_UTBE_ENABLE           (0x0020U) /* A/D converter start requests enabled during MTUn.TCNT up-count */
/* Down-Count TRGnAN Enable (DTnAE) */
#define _0000_MTU_DTAE_DISABLE          (0x0000U) /* A/D converter start request disabled during MTUn.TCNT down-count */
#define _0040_MTU_DTAE_ENABLE           (0x0040U) /* A/D converter start request enabled during MTUn.TCNT down-count */
/* Up-Count TRGnAN Enable (UTnAE) */
#define _0000_MTU_UTAE_DISABLE          (0x0000U) /* A/D converter start requests disabled during MTUn.TCNT up-count */
#define _0080_MTU_UTAE_ENABLE           (0x0080U) /* A/D converter start requests enabled during MTUn.TCNT up-count */
/* MTUn.TADCOBRA/B Transfer Timing Select (BF[1:0]) (n=4,7) */
#define _0000_MTU_BF_DISABLE            (0x0000U) /* Transfers data from buffer register is disabled */
#define _4000_MTU_BF_TOP                (0x4000U) /* Transfers data at the crest of the MTUn.TCNT count */
#define _8000_MTU_BF_LOW                (0x8000U) /* Transfers data at the trough of the MTUn.TCNT count */
#define _C000_MTU_BF_BOTH               (0xC000U) /* Transfers data at the crest and trough of the MTUn.TCNT count */
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
