Kageyana/RX671_MCR/RX671_MCR/src/WS2812C.c

//====================================//
// インクルード
//====================================//
#include "WS2812C.h"
#include "r_dmaca_rx_if.h"
#include "sys/types.h"
#include <stdbool.h>
#include <stdint.h>
//====================================//
// グローバル変数の宣言
//====================================//
uint8_t LED_Data[MAX_LED][4];
volatile static uint8_t pwmData[(24 * MAX_LED) + RESET_LEN] = {0};
volatile bool datasentflag = false;
volatile bool dma_done_flag = true;
volatile bool lineflag = false;

dmaca_transfer_data_cfg_t td_cfg;
dmaca_stat_t dmac_status;
///////////////////////////////////////////////////////////////////////////
// モジュール名 initLED
// 処理概要     LEDの初期化
// 引数         なし
// 戻り値       なし
///////////////////////////////////////////////////////////////////////////
void initLED(void)
{
	volatile dmaca_return_t retDMA;
	

	retDMA = R_DMACA_Open(DMACA_CH0); // DMAC0をオープン
	retDMA = R_DMACA_Int_Callback(DMACA_CH0,ledDMAinterrupt); // DMAC0の割り込みコールバック関数設定
	retDMA = R_DMACA_Int_Enable(DMACA_CH0,15);	 // 割り込み優先度を設定

	// TPU5.TGRB = PWM_MAX;
	// R_Config_TPU5_Start();   // PWM出力スタート

	
	// sendLED();

}
///////////////////////////////////////////////////////////////////////////
// モジュール名 ledDMAinterrupt
// 処理概要     DMA割り込みハンドラ
// 引数         なし
// 戻り値       なし
///////////////////////////////////////////////////////////////////////////
void ledDMAinterrupt(void)
{
	volatile dmaca_return_t retDMA;
    if (DMAC0.DMSTS.BIT.DTIF == 1U)
    {	
		R_Config_SCI0_Stop(); // SCI0をストップ
		retDMA = R_DMACA_Control(DMACA_CH0, DMACA_CMD_ESIF_STATUS_CLR, &dmac_status); // DMAエスケープフラグクリア
		retDMA = R_DMACA_Control(DMACA_CH0, DMACA_CMD_DTIF_STATUS_CLR, &dmac_status); // DMA転送完了フラグクリア
		datasentflag = false; 	// データ送信フラグをクリア
		
    }
}
///////////////////////////////////////////////////////////////////////////
// モジュール名 setLED
// 処理概要     色ごとの輝度を設定する
// 引数         LEDnum:設定するLEDの番号(0から) rgb:色ごとの輝度(0～255)
// 戻り値       なし
///////////////////////////////////////////////////////////////////////////
void setLED(uint8_t LEDnum, uint8_t Red, uint8_t Green, uint8_t Blue)
{
    if (!datasentflag) {
        LED_Data[LEDnum][0] = LEDnum;
        LED_Data[LEDnum][1] = Green;
        LED_Data[LEDnum][2] = Red;
        LED_Data[LEDnum][3] = Blue;
    }
}
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
